phiph-s/LAYR-GuardianChip/src/hsrm_team1.sv

// SPDX-FileCopyrightText: © 2025 LibreLane Template Contributors
// SPDX-License-Identifier: Apache-2.0

`default_nettype none

module hsrmteam1  #(
    // Power/ground pads for core
    parameter NUM_VDD_PADS = 2,
    parameter NUM_VSS_PADS = 2,

    // Power/ground pads for I/O
    parameter NUM_IOVDD_PADS = 1,
    parameter NUM_IOVSS_PADS = 1,

    // Signal pads
    parameter NUM_INPUT_PADS  = 3,
    parameter NUM_OUTPUT_PADS = 13,
    parameter NUM_BIDIR_PADS  = 0,
    parameter NUM_ANALOG_PADS = 0
    )(
    `ifdef USE_POWER_PINS
    inout wire IOVDD,
    inout wire IOVSS,
    inout wire VDD,
    inout wire VSS,
    `endif
    inout  wire clk_PAD,
    inout  wire rst_n_PAD,
    inout  wire [NUM_INPUT_PADS-1 :0] input_PAD,
    inout  wire [NUM_OUTPUT_PADS-1:0] output_PAD
);

    wire clk_PAD2CORE;
    wire rst_n_PAD2CORE;
    wire [NUM_INPUT_PADS-1 :0] input_PAD2CORE;
    wire [NUM_OUTPUT_PADS-1:0] output_CORE2PAD;

    // Power/ground pad instances
    generate
    for (genvar i=0; i<NUM_IOVDD_PADS; i++) begin : iovdd_pads
        (* keep *)
        sg13g2_IOPadIOVdd iovdd_pad (
            `ifdef USE_POWER_PINS
            .iovdd  (IOVDD),
            .iovss  (IOVSS),
            .vdd    (VDD),
            .vss    (VSS)
            `endif
        );
    end
    for (genvar i=0; i<NUM_IOVSS_PADS; i++) begin : iovss_pads
        (* keep *)
        sg13g2_IOPadIOVss iovss_pad (
            `ifdef USE_POWER_PINS
            .iovdd  (IOVDD),
            .iovss  (IOVSS),
            .vdd    (VDD),
            .vss    (VSS)
            `endif
        );
    end
    for (genvar i=0; i<NUM_VDD_PADS; i++) begin : vdd_pads
        (* keep *)
        sg13g2_IOPadVdd vdd_pad (
            `ifdef USE_POWER_PINS
            .iovdd  (IOVDD),
            .iovss  (IOVSS),
            .vdd    (VDD),
            .vss    (VSS)
            `endif
        );
    end
    for (genvar i=0; i<NUM_VSS_PADS; i++) begin : vss_pads
        (* keep *)
        sg13g2_IOPadVss vss_pad (
            `ifdef USE_POWER_PINS
            .iovdd  (IOVDD),
            .iovss  (IOVSS),
            .vdd    (VDD),
            .vss    (VSS)
            `endif
        );
    end
    endgenerate

    // Signal IO pad instances

    (* keep *)
    sg13g2_IOPadIn clk_pad (
        `ifdef USE_POWER_PINS
        .iovdd  (IOVDD),
        .iovss  (IOVSS),
        .vdd    (VDD),
        .vss    (VSS),
        `endif
        .p2c    (clk_PAD2CORE),
        .pad    (clk_PAD)
    );

    (* keep *)
    sg13g2_IOPadIn rst_n_pad (
        `ifdef USE_POWER_PINS
        .iovdd  (IOVDD),
        .iovss  (IOVSS),
        .vdd    (VDD),
        .vss    (VSS),
        `endif
        .p2c    (rst_n_PAD2CORE),
        .pad    (rst_n_PAD)
    );

    generate
    for (genvar i=0; i<NUM_INPUT_PADS; i++) begin : inputs
        (* keep *)
        sg13g2_IOPadIn input_pad (
            `ifdef USE_POWER_PINS
            .iovdd  (IOVDD),
            .iovss  (IOVSS),
            .vdd    (VDD),
            .vss    (VSS),
            `endif
            .p2c    (input_PAD2CORE[i]),
            .pad    (input_PAD[i])
        );
    end
    endgenerate

    generate
    for (genvar i=0; i<NUM_OUTPUT_PADS; i++) begin : outputs
        (* keep *)
        sg13g2_IOPadOut30mA output_pad (
            `ifdef USE_POWER_PINS
            .iovdd  (IOVDD),
            .iovss  (IOVSS),
            .vdd    (VDD),
            .vss    (VSS),
            `endif
            .c2p    (output_CORE2PAD[i]),
            .pad    (output_PAD[i])
        );
    end
    endgenerate


    // Core design

    (* keep *) chip_core #(
        .NUM_INPUT_PADS  (NUM_INPUT_PADS),
        .NUM_OUTPUT_PADS (NUM_OUTPUT_PADS),
        .NUM_BIDIR_PADS  (NUM_BIDIR_PADS),
        .NUM_ANALOG_PADS (NUM_ANALOG_PADS)
    ) i_chip_core (
        .clk        (clk_PAD2CORE),
        .rst_n      (rst_n_PAD2CORE),
        .input_in   (input_PAD2CORE),
        .output_out (output_CORE2PAD)
    );

endmodule

`default_nettype wire
